vives-project-xp/low-voltage-UPS/case/blender/render/background/frames/0159.png

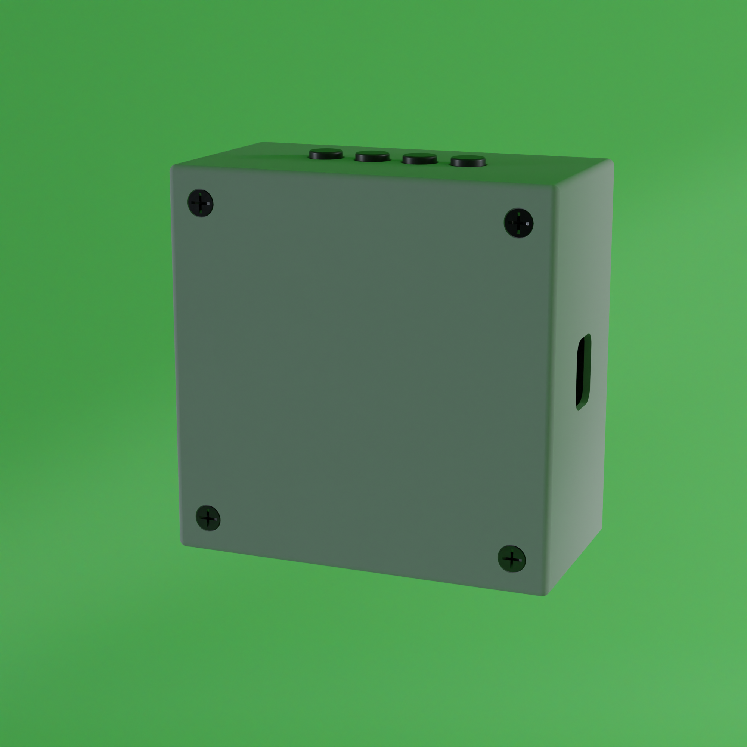
case/blender/render/background/frames/0159.png
