vives-project-xp/low-voltage-UPS/case/blender/render/background/frames/0164.png

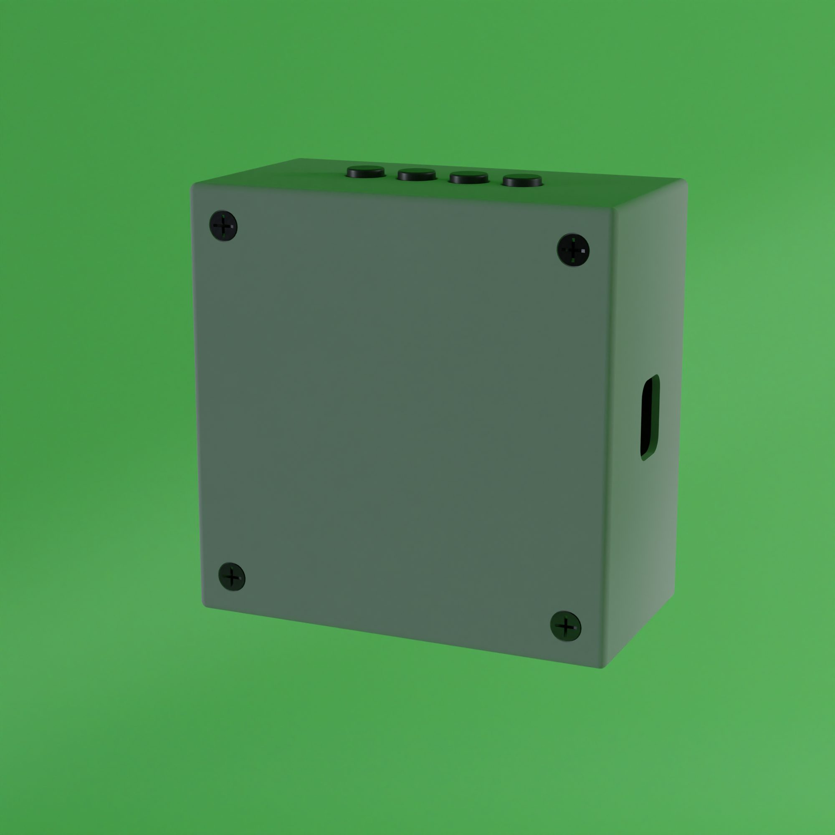
case/blender/render/background/frames/0164.png
