vives-project-xp/low-voltage-UPS/case/blender/render/background/frames/0172.png

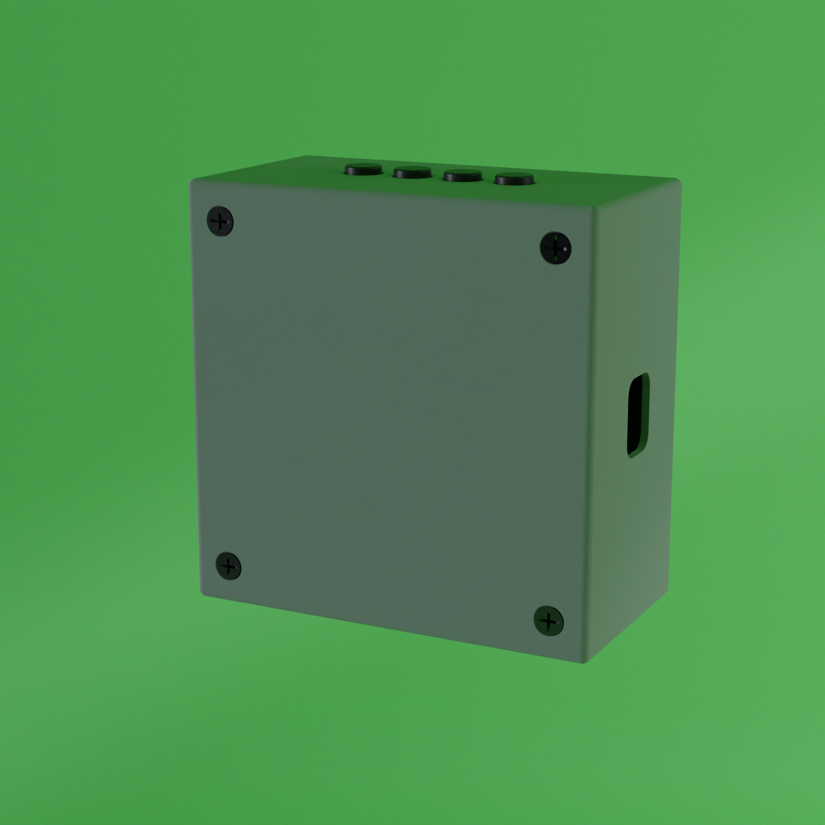
case/blender/render/background/frames/0172.png
