vives-project-xp/low-voltage-UPS/case/blender/render/transparent/30fps.gif

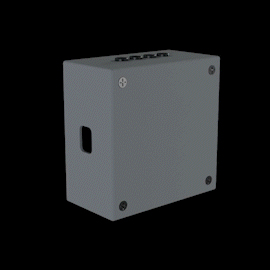
case/blender/render/transparent/30fps.gif
